jeffdhooton/squat-astrograph/images/IMG_2207.jpeg

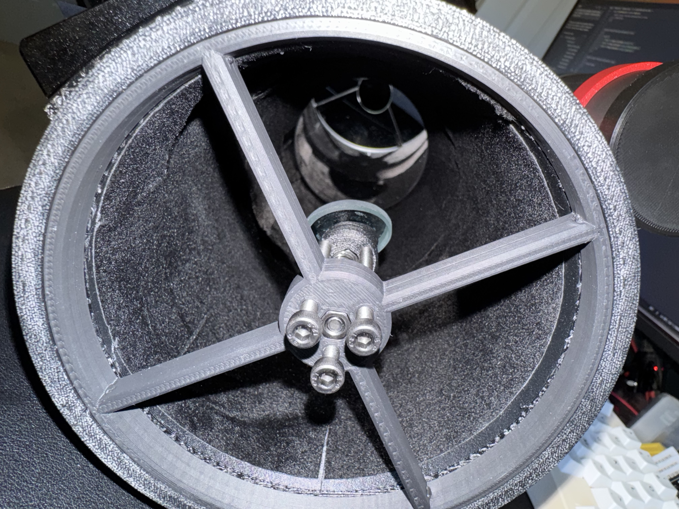
images/IMG_2207.jpeg
