jeffdhooton/squat-astrograph/images/IMG_2208.jpeg

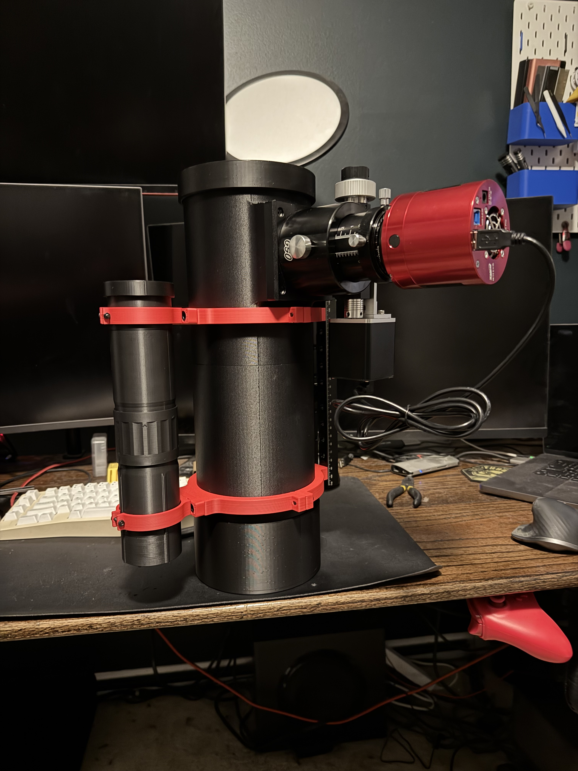
images/IMG_2208.jpeg
